re-innovation/LatrineLogger/PCB/Latrine Logger PCB v1/555sensorUnit/555sensor.sch

## KiCad design PCB/Latrine Logger PCB v1/555sensorUnit/555sensor.sch (2016-06-12)

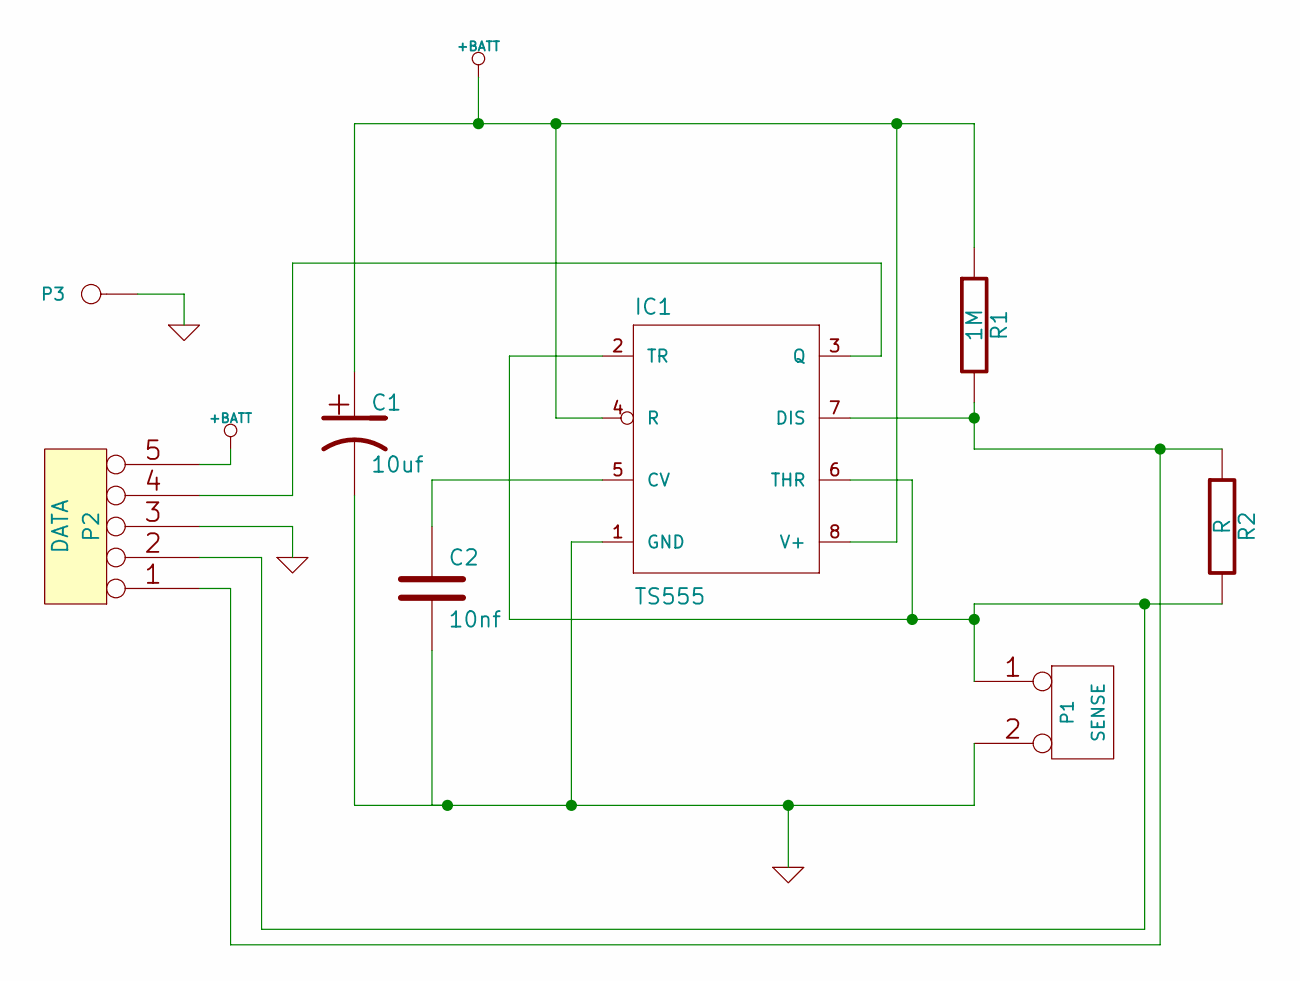
[picture p24: schematic 555sensor.sch]

Parts:
C1: 10uf
C2: 10nf
IC1: TS555; linear2-DIL08
P1: SENSE
P2: DATA
P3: GND
R1: 1M
R2: R

Connections:
+BATT: C1.1, IC1.4 (R), IC1.8 (V+), P2.5, R1.1
GND: C1.2, C2.2, IC1.1 (GND), P1.2 (PM), P2.3, P3.1
unnamed: C2.1, IC1.5 (CV)
unnamed: IC1.2 (TR), IC1.6 (THR), P1.1, P2.2, R2.2
unnamed: IC1.3 (Q), P2.4
unnamed: IC1.7 (DIS), P2.1, R1.2, R2.1
