re-innovation/LatrineLogger/PCB/Latrine Logger PCB v1/LatrineLoggerMainUnit/ArduinoUno.sch

## KiCad design PCB/Latrine Logger PCB v1/LatrineLoggerMainUnit/ArduinoUno.sch (2016-06-12)

Schematic: ArduinoUno.sch

Parts:
C1: 100uF
C2, C3: 100nF
C4, C5: 22pF
D3: 1N4001
IC1: ATMEGA328P-A; TQFP32
P11: PWR_JMP
P12: ISP
P13: FTDI
P14: SERIAL
R8: 10k
SHIELD1: ARDUINO_SHIELD
SW2: RESET
X1: 16MHz

Notes on the sheet:
1: RTS# 2: Rx 3: Tx 4: Vcc 5: CTS# 6: GND
OUTPUT FOR SERIAL/USB
JUMPER REQUIRED FOR EXTENAL POWER
1: 3.3V 2: RST 3: Vcc 4: TxD 5: RxD 6: GND
