re-innovation/LatrineLogger/PCB/Latrine Logger PCB v1/LatrineLoggerMainUnit/GSMmodule.sch

## KiCad design PCB/Latrine Logger PCB v1/LatrineLoggerMainUnit/GSMmodule.sch (2016-06-12)

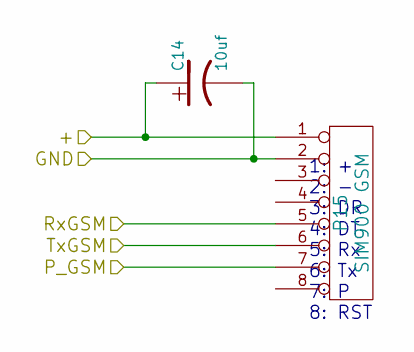
[picture p25: schematic GSMmodule.sch]

Parts:
C14: 10uf
P15: SIM900 GSM

Connections:
+: C14.1, P15.1
GND: C14.2, P15.2
P_GSM: P15.7
RxGSM: P15.5
TxGSM: P15.6

Notes on the sheet:
1: + 2: - 3: DR 4: DT 5: Rx 6: Tx 7: P 8: RST
