re-innovation/LatrineLogger/PCB/Latrine Logger PCB v1/LatrineLoggerMainUnit/LatrineLoggerPCB.sch

## KiCad design PCB/Latrine Logger PCB v1/LatrineLoggerMainUnit/LatrineLoggerPCB.sch (2016-06-12)

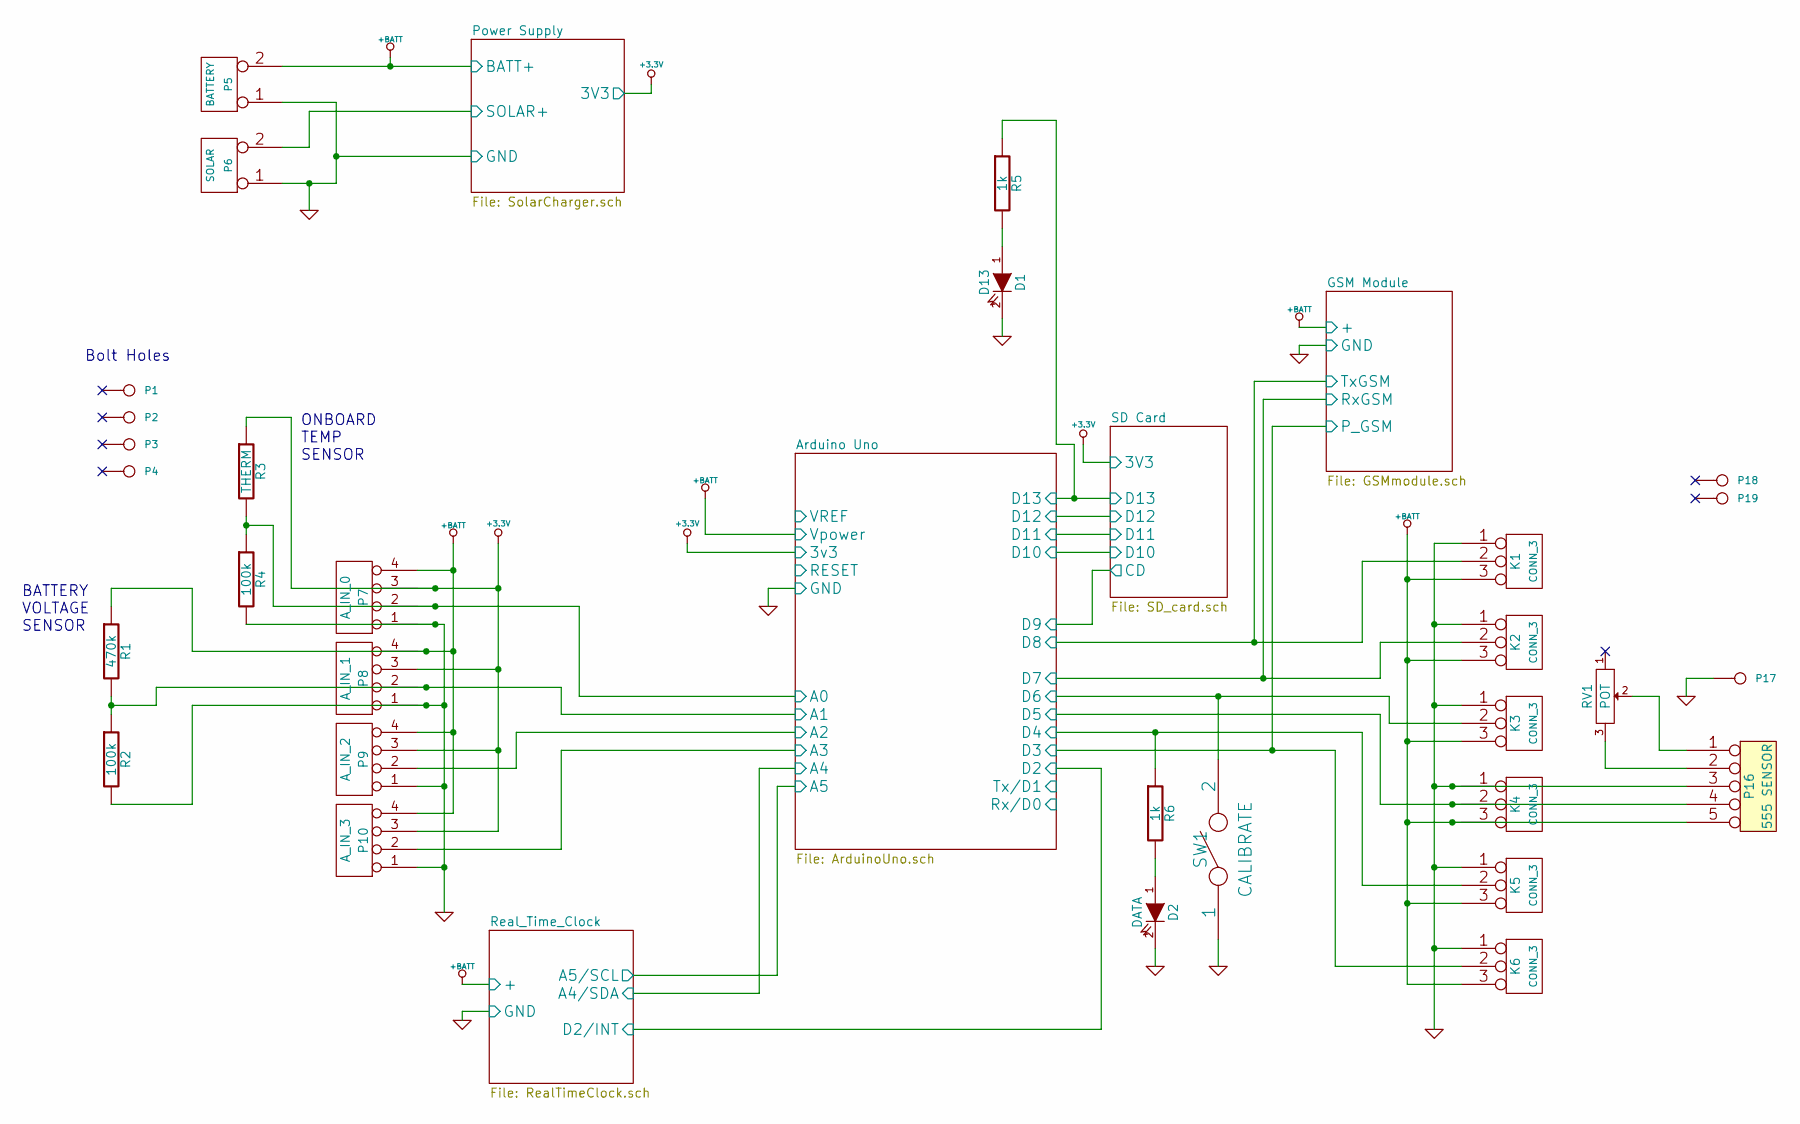
[picture p26: schematic LatrineLoggerPCB.sch]

Parts:
D1: D13
D2: DATA
K1, K2, K3, K4, K5, K6: CONN_3
P1, P2, P3, P4, P18, P19: CONN_1
P5: BATTERY
P6: SOLAR
P7: A_IN_0
P8: A_IN_1
P9: A_IN_2
P10: A_IN_3
P16: 555 SENSOR
P17: GND
R1: 470k
R2, R4: 100k
R3: THERM
R5, R6: 1k
RV1: POT
SW1: CALIBRATE

Connections:
+3.3V: P7.3, P8.3, P9.3, P10.3, R3.1
+BATT: K1.3, K2.3, K3.3, K4.3, K5.3, K6.3, P5.2 (PM), P7.4, P8.4, P9.4, P10.4, P16.5, R1.1
A0: P7.2, R3.2, R4.1
A1: P8.2, R1.2, R2.1
A2: P9.2
A3: P10.2
D3: K6.2 (PM)
D4: K5.2 (PM), R6.1
D5: K4.2 (PM), P16.4
D6: K3.2 (PM), SW1.2
D7: K2.2 (PM)
D8: K1.2 (PM)
D13: R5.1
GND: D1.2 (K), D2.2 (K), K1.1, K2.1, K3.1, K4.1, K5.1, K6.1, P5.1, P6.1, P7.1, P8.1, P9.1, P10.1, P16.3, P17.1, R2.2, R4.2, SW1.1
unnamed: D1.1 (A), R5.2
unnamed: D2.1 (A), R6.2
unnamed: P16.1, RV1.2
unnamed: P16.2, RV1.3
SOLAR+: P6.2 (PM)

Notes on the sheet:
Bolt Holes
ONBOARD TEMP SENSOR
BATTERY VOLTAGE SENSOR
