re-innovation/LatrineLogger/PCB/Latrine Logger PCB v1/LatrineLoggerMainUnit/RealTimeClock.sch

## KiCad design PCB/Latrine Logger PCB v1/LatrineLoggerMainUnit/RealTimeClock.sch (2016-06-12)

Schematic: RealTimeClock.sch

Parts:
BT1: CR2032 3V BATT
C6: 10uF
C7: CTRIM
D4, D5: 1N4148
R9, R10: 10k
U2: PCF8563
X2: 32.768kHz
