re-innovation/LatrineLogger/PCB/Latrine Logger PCB v1/LatrineLoggerMainUnit/SD_card.sch

## KiCad design PCB/Latrine Logger PCB v1/LatrineLoggerMainUnit/SD_card.sch (2016-06-12)

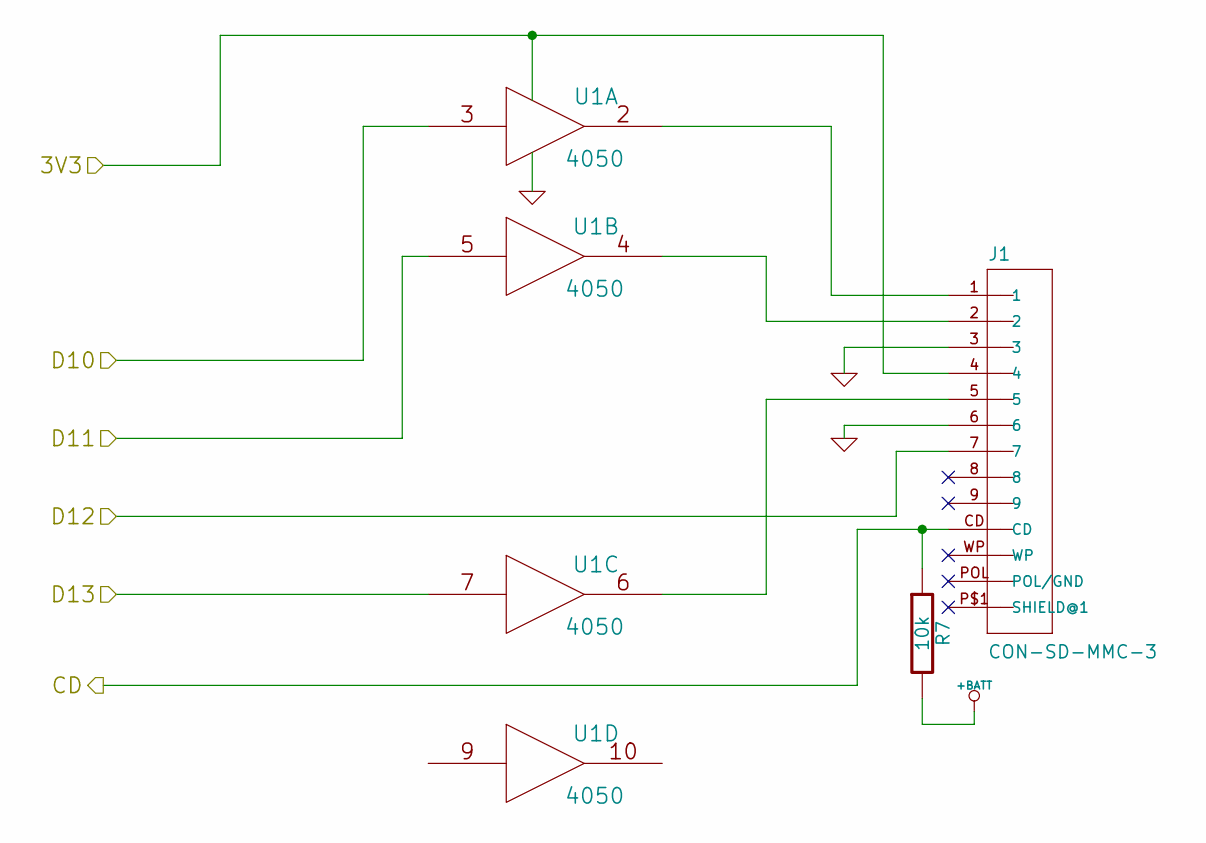
[picture p27: schematic SD_card.sch]

Parts:
J1: CON-SD-MMC-3; m-pad-2.1-DM1AA-SF-PEJ(21)
R7: 10k
U1: 4050

Connections:
3V3: J1.4, U1.1 (VCC)
+BATT: R7.2
CD: J1.CD, R7.1
D10: U1.3
D11: U1.5
D12: J1.7
D13: U1.7
GND: J1.3, J1.6, U1.8 (VSS)
unnamed: J1.1, U1.2
unnamed: J1.2, U1.4
unnamed: J1.5, U1.6
