re-innovation/LatrineLogger/PCB/Latrine Logger PCB v1/LatrineLoggerMainUnit/SolarCharger.sch

## KiCad design PCB/Latrine Logger PCB v1/LatrineLoggerMainUnit/SolarCharger.sch (2016-06-12)

Schematic: SolarCharger.sch

Parts:
C8: 4.7uf
C9: >10uf
C10: 1uf
C11: 10uf
C12, C13: 10uF
L1: 10uH
R11: 40.2k
R12: 1020k
R13: 332k
U3: LTC3105_MSOP
U4: MCP1703
